antmicro/quickfeather-dev-board/assets/previews/layer1.png

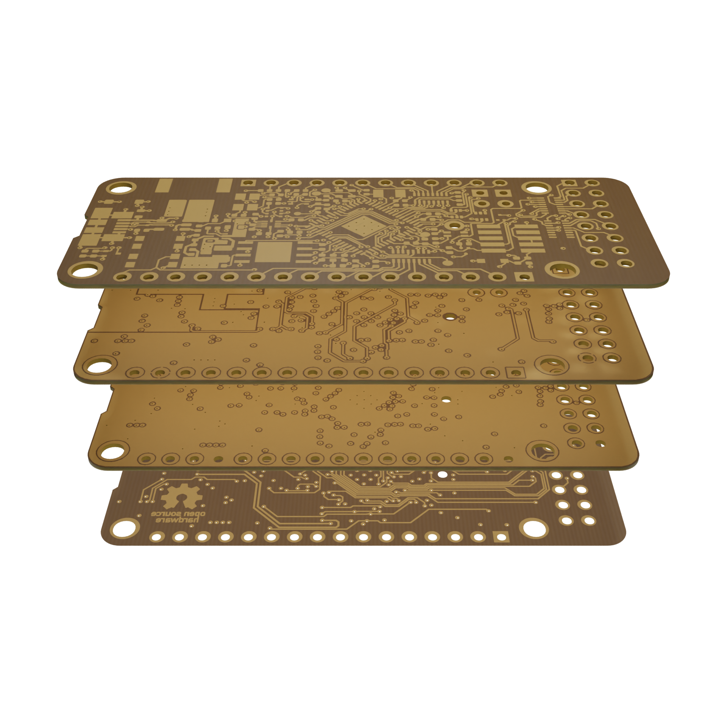
assets/previews/layer1.png
