antmicro/quickfeather-dev-board/assets/previews/layer2.png

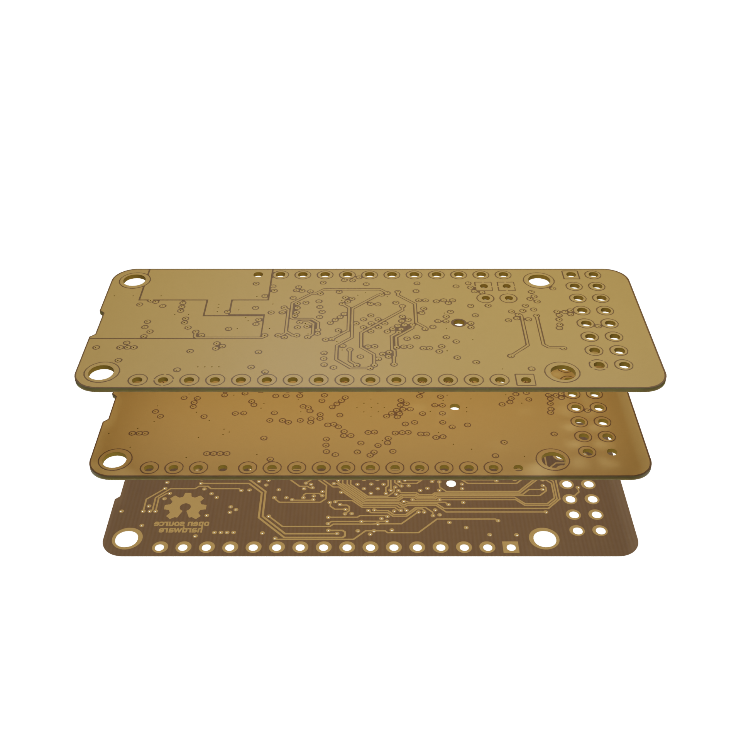
assets/previews/layer2.png
