antmicro/quickfeather-dev-board/assets/previews/layer3.png

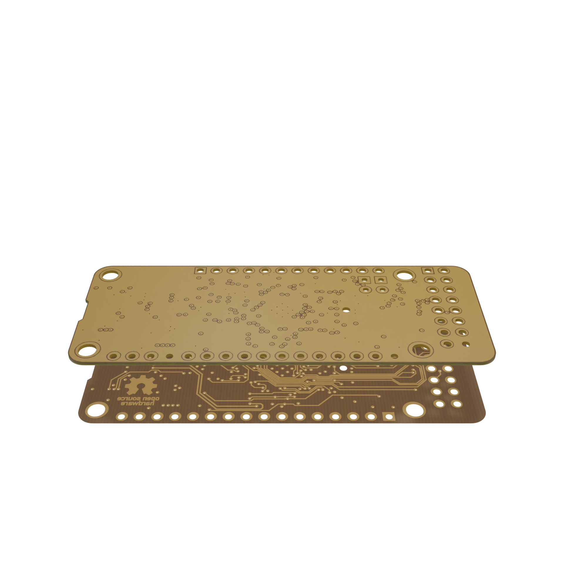
assets/previews/layer3.png
