antmicro/quickfeather-dev-board/assets/previews/leftB.png

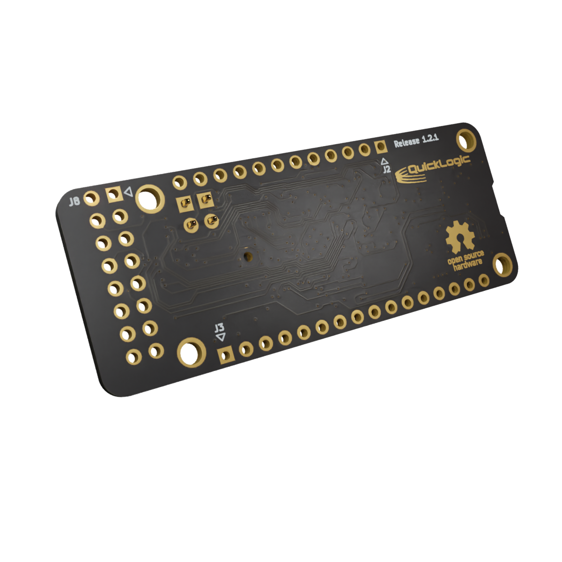
assets/previews/leftB.png
