antmicro/quickfeather-dev-board/assets/previews/orthoB.png

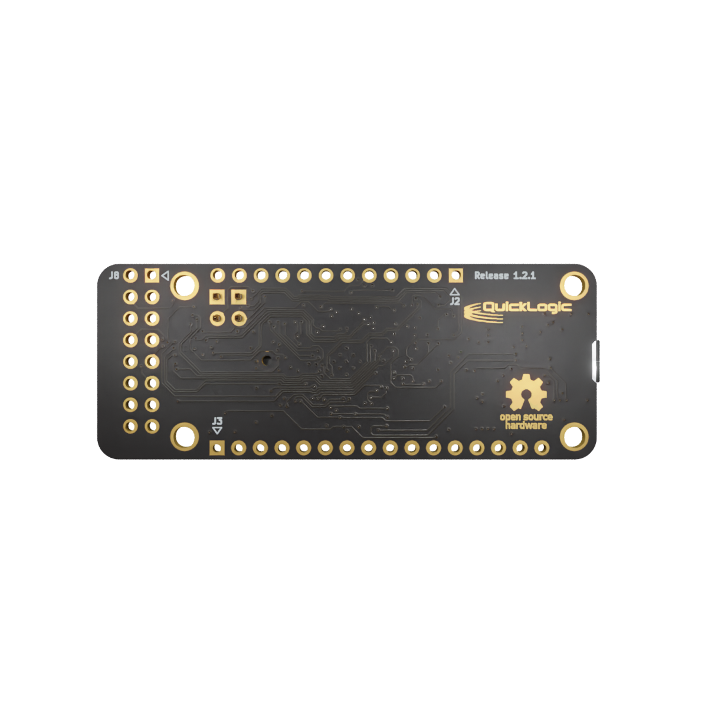
assets/previews/orthoB.png
