antmicro/quickfeather-dev-board/assets/previews/orthoT.png

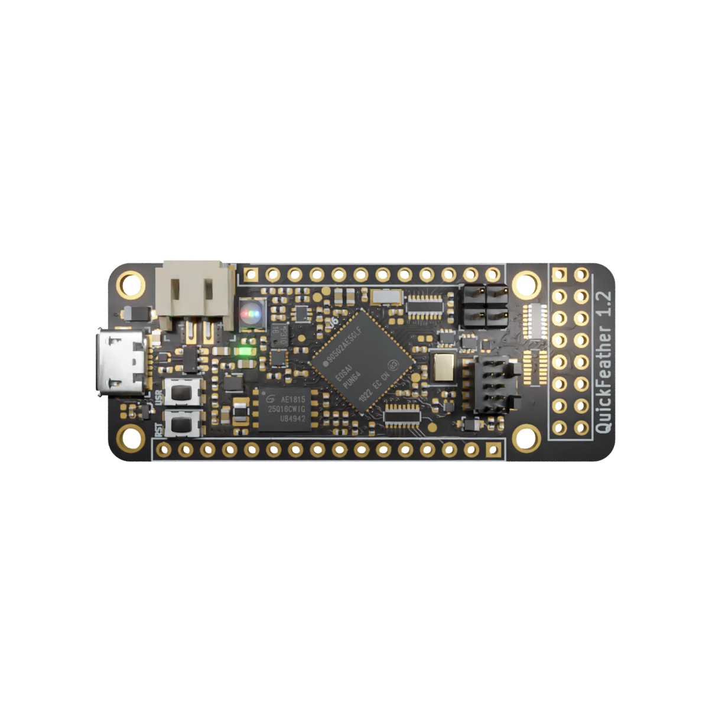
assets/previews/orthoT.png
