antmicro/quickfeather-dev-board/assets/previews/photoB.png

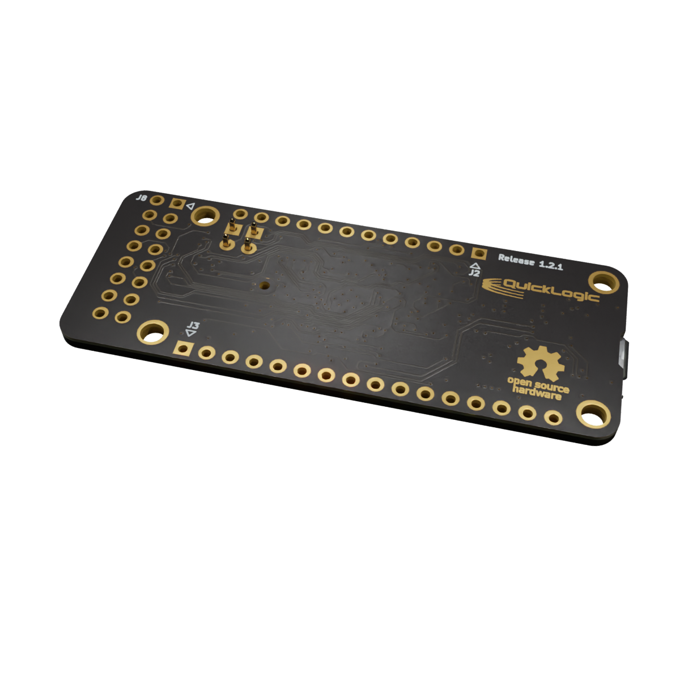
assets/previews/photoB.png
