antmicro/quickfeather-dev-board/assets/previews/rightB.png

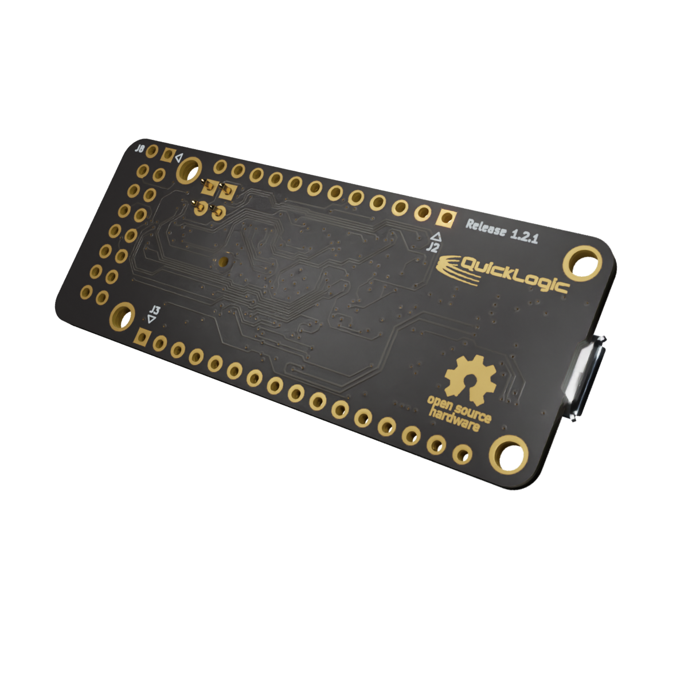
assets/previews/rightB.png
